MelexinVN/bs_kombo_bs/media/photo_2024-06-19_20-01-25.jpg

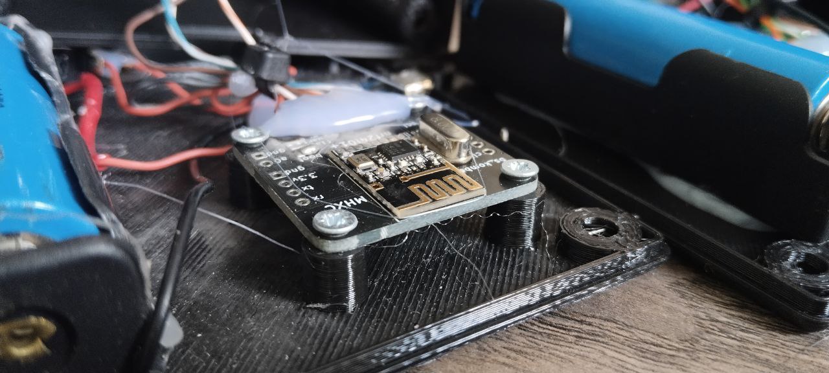
media/photo_2024-06-19_20-01-25.jpg
