MelexinVN/bs_kombo_bs/media/photo_2024-06-20_09-03-27.jpg

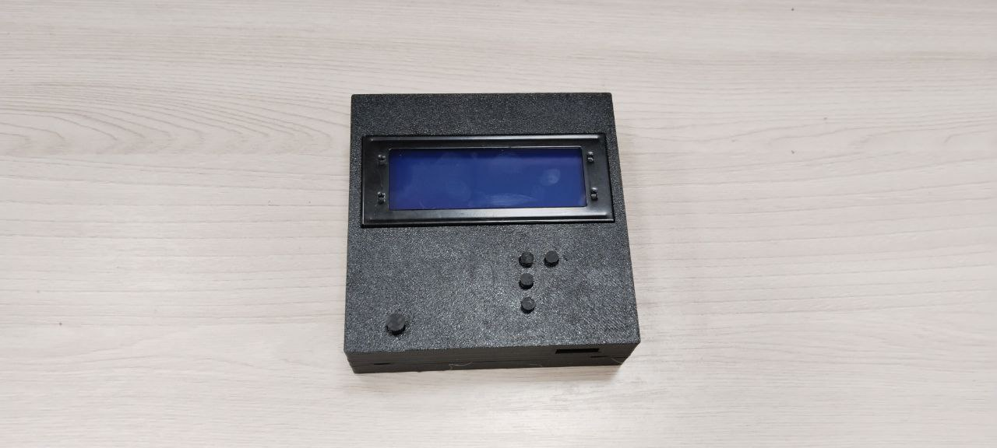
media/photo_2024-06-20_09-03-27.jpg
