MelexinVN/bs_kombo_bs/soft/Visual Studio/mozgocolco_v.2.0/images/03.png

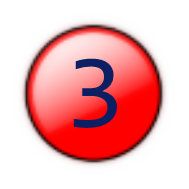
soft/Visual Studio/mozgocolco_v.2.0/images/03.png
