MelexinVN/bs_kombo_bs/soft/Visual Studio/mozgocolco_v.2.0/images/06.png

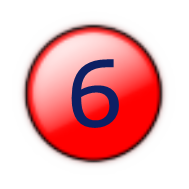
soft/Visual Studio/mozgocolco_v.2.0/images/06.png
