MelexinVN/bs_kombo_bs/soft/Visual Studio/mozgocolco_v.2.0/images/info-2-xxl.png

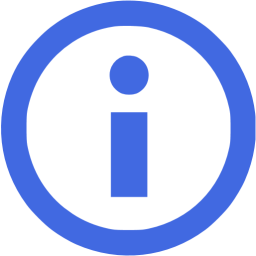
soft/Visual Studio/mozgocolco_v.2.0/images/info-2-xxl.png
