MelexinVN/bs_kombo_bs/3d/button_box_v.1.1 (80mm)/button_box_v.1.1_verh.stl

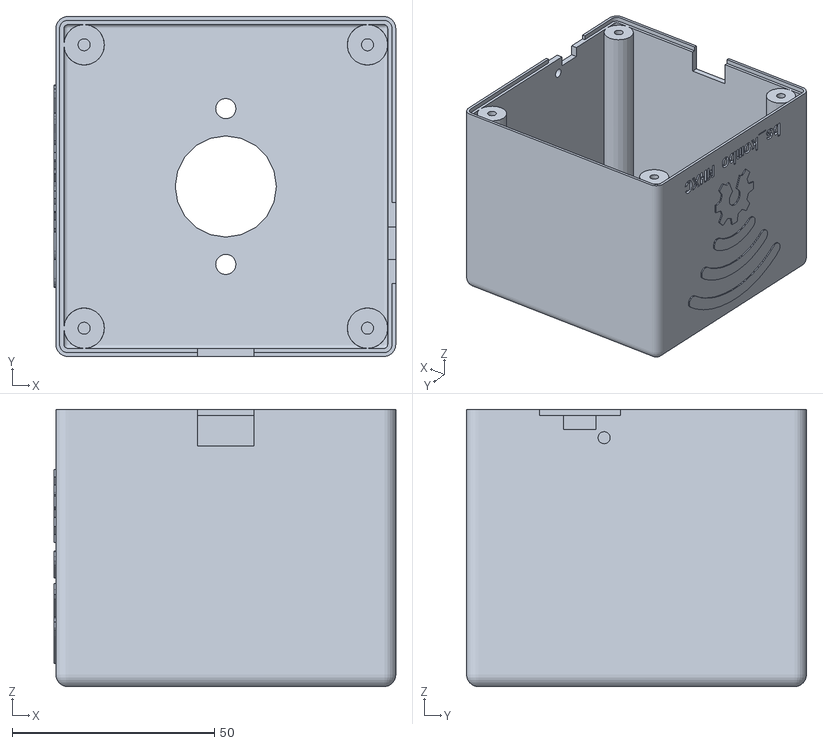
[picture p59: CAD file, 2024-08-23, an earlier design]
3d/button_box_v.1.1 (80mm)/button_box_v.1.1_verh.stl
84.4 x 84.0 x 68.5
