MelexinVN/bs_kombo_bs/soft/Keil uVision/bs_base_v.1.04/Core/Inc/lcd.h

#ifndef LCD_H_
#define LCD_H_
//------------------------------------------------
#include "main.h"
//------------------------------------------------
#define e_set() LCD_WriteByteI2CLCD(portlcd|=0x04)  //установка линии Е в 1
#define e_reset() LCD_WriteByteI2CLCD(portlcd&=~0x04) //установка линии Е в 0
#define rs_set() LCD_WriteByteI2CLCD(portlcd|=0x01) //установка линии RS в 1
#define rs_reset() LCD_WriteByteI2CLCD(portlcd&=~0x01) //установка линии RS в 0
#define setled() LCD_WriteByteI2CLCD(portlcd|=0x08) //установка линии RS в 1
#define setwrite() LCD_WriteByteI2CLCD(portlcd&=~0x02) //установка линии RS в 0
//------------------------------------------------
void LCD_init(void);
void LCD_Clear(void);
void LCD_SendChar(char ch);
void LCD_String(char* st);
void LCD_SetPos(uint8_t x, uint8_t y);
//------------------------------------------------
#endif /* LCD_H_ */
